pabloqb2000/py-rubik_solver/src/cubes/configs.py

from vpython import color, vector

'''
    Colors
'''
bg_color = color.black
base_color = color.gray(0.4)
colors_dict_def = {
    "U": color.white,
    "F": color.red,
    "R": color.blue,
    "B": color.orange,
    "L": color.green,
    "D": color.yellow,
}

'''
    Sizes
'''
box_margin = 0.15
box_height = 0.2

'''
    Times
'''
fps_def = 30
move_time_def = 2
wait_time_def = 0.8
speed = 1

move_time_def /= speed
wait_time_def /= speed

'''
    Color detection
'''
detection_radius_def = 2
